jazamatronic/nucleo_adsr/Core/Src/envelope.c

/*
 * MIT License
 *
 * Copyright (c) 2021 Jared Anderson
 *
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
 * THE SOFTWARE IS PROVIDED "AS IS", WITHOUT WARRANTY OF ANY KIND, EXPRESS OR
 * IMPLIED, INCLUDING BUT NOT LIMITED TO THE WARRANTIES OF MERCHANTABILITY,
 * FITNESS FOR A PARTICULAR PURPOSE AND NONINFRINGEMENT. IN NO EVENT SHALL THE
 * AUTHORS OR COPYRIGHT HOLDERS BE LIABLE FOR ANY CLAIM, DAMAGES OR OTHER
 * LIABILITY, WHETHER IN AN ACTION OF CONTRACT, TORT OR OTHERWISE, ARISING FROM,
 * OUT OF OR IN CONNECTION WITH THE SOFTWARE OR THE USE OR OTHER DEALINGS IN THE
 * SOFTWARE.
 */

#include "envelope.h"

// tclsh for linear segment: for {set i 1} { $i <= 256 } { incr i } { puts [format "0x%03x" [expr int(($i / 256.0) * 4095)]] }
//           exp    segment: for {set i 1} { $i <= 256 } { incr i } { puts [format "0x%03x" [expr int(pow(4095, ($i / 256.0)))]] }
//           log    segment: for {set i 1} { $i <= 256 } { incr i } { puts [format "0x%03x" [expr int(log10(1 + (9 * ($i/256.0))) * 4095)]] }
static uint16_t adsr_curves[NUM_CURVES][ADSR_TABLE_LEN] = { \
  {0x00f, 0x01f, 0x02f, 0x03f, 0x04f, 0x05f, 0x06f, 0x07f, 0x08f, 0x09f, 0x0af, \
  0x0bf, 0x0cf, 0x0df, 0x0ef, 0x0ff, 0x10f, 0x11f, 0x12f, 0x13f, 0x14f, 0x15f, \
  0x16f, 0x17f, 0x18f, 0x19f, 0x1af, 0x1bf, 0x1cf, 0x1df, 0x1ef, 0x1ff, 0x20f, \
  0x21f, 0x22f, 0x23f, 0x24f, 0x25f, 0x26f, 0x27f, 0x28f, 0x29f, 0x2af, 0x2bf, \
  0x2cf, 0x2df, 0x2ef, 0x2ff, 0x30f, 0x31f, 0x32f, 0x33f, 0x34f, 0x35f, 0x36f, \
  0x37f, 0x38f, 0x39f, 0x3af, 0x3bf, 0x3cf, 0x3df, 0x3ef, 0x3ff, 0x40f, 0x41f, \
  0x42f, 0x43f, 0x44f, 0x45f, 0x46f, 0x47f, 0x48f, 0x49f, 0x4af, 0x4bf, 0x4cf, \
  0x4df, 0x4ef, 0x4ff, 0x50f, 0x51f, 0x52f, 0x53f, 0x54f, 0x55f, 0x56f, 0x57f, \
  0x58f, 0x59f, 0x5af, 0x5bf, 0x5cf, 0x5df, 0x5ef, 0x5ff, 0x60f, 0x61f, 0x62f, \
  0x63f, 0x64f, 0x65f, 0x66f, 0x67f, 0x68f, 0x69f, 0x6af, 0x6bf, 0x6cf, 0x6df, \
  0x6ef, 0x6ff, 0x70f, 0x71f, 0x72f, 0x73f, 0x74f, 0x75f, 0x76f, 0x77f, 0x78f, \
  0x79f, 0x7af, 0x7bf, 0x7cf, 0x7df, 0x7ef, 0x7ff, 0x80f, 0x81f, 0x82f, 0x83f, \
  0x84f, 0x85f, 0x86f, 0x87f, 0x88f, 0x89f, 0x8af, 0x8bf, 0x8cf, 0x8df, 0x8ef, \
  0x8ff, 0x90f, 0x91f, 0x92f, 0x93f, 0x94f, 0x95f, 0x96f, 0x97f, 0x98f, 0x99f, \
  0x9af, 0x9bf, 0x9cf, 0x9df, 0x9ef, 0x9ff, 0xa0f, 0xa1f, 0xa2f, 0xa3f, 0xa4f, \
  0xa5f, 0xa6f, 0xa7f, 0xa8f, 0xa9f, 0xaaf, 0xabf, 0xacf, 0xadf, 0xaef, 0xaff, \
  0xb0f, 0xb1f, 0xb2f, 0xb3f, 0xb4f, 0xb5f, 0xb6f, 0xb7f, 0xb8f, 0xb9f, 0xbaf, \
  0xbbf, 0xbcf, 0xbdf, 0xbef, 0xbff, 0xc0f, 0xc1f, 0xc2f, 0xc3f, 0xc4f, 0xc5f, \
  0xc6f, 0xc7f, 0xc8f, 0xc9f, 0xcaf, 0xcbf, 0xccf, 0xcdf, 0xcef, 0xcff, 0xd0f, \
  0xd1f, 0xd2f, 0xd3f, 0xd4f, 0xd5f, 0xd6f, 0xd7f, 0xd8f, 0xd9f, 0xdaf, 0xdbf, \
  0xdcf, 0xddf, 0xdef, 0xdff, 0xe0f, 0xe1f, 0xe2f, 0xe3f, 0xe4f, 0xe5f, 0xe6f, \
  0xe7f, 0xe8f, 0xe9f, 0xeaf, 0xebf, 0xecf, 0xedf, 0xeef, 0xeff, 0xf0f, 0xf1f, \
  0xf2f, 0xf3f, 0xf4f, 0xf5f, 0xf6f, 0xf7f, 0xf8f, 0xf9f, 0xfaf, 0xfbf, 0xfcf, \
  0xfdf, 0xfef, 0xfff }, \
  {0x001, 0x001, 0x001, 0x001, 0x001, 0x001, 0x001, 0x001, 0x001, 0x001, 0x001, \
  0x001, 0x001, 0x001, 0x001, 0x001, 0x001, 0x001, 0x001, 0x001, 0x001, 0x002, \
  0x002, 0x002, 0x002, 0x002, 0x002, 0x002, 0x002, 0x002, 0x002, 0x002, 0x002, \
  0x003, 0x003, 0x003, 0x003, 0x003, 0x003, 0x003, 0x003, 0x003, 0x004, 0x004, \
  0x004, 0x004, 0x004, 0x004, 0x004, 0x005, 0x005, 0x005, 0x005, 0x005, 0x005, \
  0x006, 0x006, 0x006, 0x006, 0x007, 0x007, 0x007, 0x007, 0x007, 0x008, 0x008, \
  0x008, 0x009, 0x009, 0x009, 0x00a, 0x00a, 0x00a, 0x00b, 0x00b, 0x00b, 0x00c, \
  0x00c, 0x00d, 0x00d, 0x00d, 0x00e, 0x00e, 0x00f, 0x00f, 0x010, 0x010, 0x011, \
  0x012, 0x012, 0x013, 0x013, 0x014, 0x015, 0x015, 0x016, 0x017, 0x018, 0x018, \
  0x019, 0x01a, 0x01b, 0x01c, 0x01d, 0x01e, 0x01f, 0x020, 0x021, 0x022, 0x023, \
  0x024, 0x026, 0x027, 0x028, 0x029, 0x02b, 0x02c, 0x02e, 0x02f, 0x031, 0x032, \
  0x034, 0x036, 0x038, 0x03a, 0x03b, 0x03d, 0x03f, 0x042, 0x044, 0x046, 0x048, \
  0x04b, 0x04d, 0x050, 0x052, 0x055, 0x058, 0x05b, 0x05e, 0x061, 0x064, 0x068, \
  0x06b, 0x06f, 0x072, 0x076, 0x07a, 0x07e, 0x082, 0x087, 0x08b, 0x090, 0x094, \
  0x099, 0x09e, 0x0a4, 0x0a9, 0x0af, 0x0b4, 0x0ba, 0x0c1, 0x0c7, 0x0ce, 0x0d4, \
  0x0db, 0x0e3, 0x0ea, 0x0f2, 0x0fa, 0x102, 0x10b, 0x114, 0x11d, 0x126, 0x130, \
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
};


/*
 * process an envelope
 *
 * Walks through the phases of an ADSR in the following way:
 *
 *   Start in the idle state.  If gate is low, stay in idle.
 *   If gate is high, start the attack phase.
 *   While in the attack state, index the table until the end in the time given by attack.
 *   If gate goes low during attack phase, move directly to release.
 *   If attack finishes, move to decay state.
 *   Decay moves from max to sustain value in the given decay time
 *   If gate goes low during decay phase, move directly to release.
 *   If decay finishes, if sustain is zero move to idle, otherwise move to sustain state.
 *
 *   When an envelope is done we set the end flag to trigger other envs if needed
 *
 *   Sustain state holds that value while gate is high. On gate low move to release state
 *   In release state, move from sustain down to 0 in the time given by release.
 *   Once release is completed move to idle
 *   If gate goes high during release phase, restart the attack phase (TODO: make it restart from where it is, not 0)
 *
 *   For calculating durations - assumption is we're doing 10kHz sampling with a table length of 256 entries
 *   Time between samples will be 0.1ms so 256 entries gives 25ms or so as the fastest transition
 *   Care must be taken with an adc value of 0 - it should mean a phase_inc of a single step
 *
 *   
 *   Let's say we have full adc range = 5s (60s is tooo long)
 *   @ 10kHz that equals 50k samples 
 *
 *
 *   full scale adc = 4095
 *   table length of 256 / number of samples for 5s (50k) = 0.0512
 *   phase_inc = (4095 / <adc_value>) * 0.0512
 *
 *   doesnt return anything, the value to write to the DAC is stored in the envelope - should be 12 bit right aligned values from the tables
 *
 *   Adding loop modes which do AD loops repeat - sustain level will be used as time between repeats
 *
 *   TRIG or INV_TRIG modes - AD oneshot envelope
 *    At the end of its cycle, a triggering envelope will be used to trigger a simple AD of another envelope
 *    The triggered envelope will ignore all gate information and do a single cycle
 *    env0 triggers env1, env1 triggers env2 and env2 triggers env0 - maybe there's a way to get them in a loop, not sure
 *    The RGB led will show two of three colours to show that the envelope is in trigger mode - the selected env plus the triggering env will be lit
 *    inverted trigger mode will have the two leds, but flashing
 *   
 *   LMNC bouncing ball easter egg mode
 *    A = initial height -> full scale = 4m
 *    D = rebound -> FS = 2
 *    R = gravity -> FS = 2 * Gravity which is -9.8 ms^-2 - as we're updating at ~10kHz this should meters per 0.1ms
 *    Do the math for the height in phase, store the velocity in phase_inc - cast it into val at the end
 *    Get into bouncing ball mode by using long press and moving sustain until it's at the top of its range (blue led)
 *    Coming out of bounce goes straight to oneshot
 */
void process_env(env_gen_t *env, uint16_t gate, uint16_t trigger)
{
  // default to staying exactly where we are
  enum state next_state = env->current_state;

  // check to see if we're triggered
  if (TRIG_MODE(env) && trigger) {
    env->triggered = 1;
  }

  // clear end of env flag
  if (env->end) {
    env->end = 0;
  }

  switch (env->current_state) {

    case IDLE:
      if (!GATE(env, gate)) { 
	env->val = 0;
      } else {
	//start the ball rolling
	if (env->mode == BOUNCY) {
	  next_state = BOUNCE;
	  //attack is initial height
	  env->phase = env->adsr[ATTACK];
	  env->val = env->adsr[ATTACK]; 
	} else {
	  next_state = ATTACK;
	  env->phase = 0;	
	}
      }
      break;

    case ATTACK:
      //gate == 0 && !env->triggered
      if (!GATE(env, gate)) { 
	env->phase = (uint16_t)ADSR_TABLE_LEN - 1;
	env->release_from = env->val;
	next_state = RELEASE;
      } else {
	if (env->adsr[ATTACK] > 0) {
	  env->phase_inc = ((float32_t)ADSR_TABLE_LEN / (LONGEST_PHASE_S * ENV_SR)) * (ADC_FS / env->adsr[ATTACK]);
	} else {
	  //attack is zero, phase_inc is twice what it would be if it were one
	  env->phase_inc = ((float32_t)ADSR_TABLE_LEN / (LONGEST_PHASE_S * ENV_SR)) * 2 * ADC_FS;
	}
	env->phase += env->phase_inc;
	if (env->phase > ADSR_TABLE_LEN) {
	  env->phase = (uint16_t)ADSR_TABLE_LEN - 1;
	  env->val = ADC_FS;
	  next_state = DECAY;
	} else {
	  env->val = interp_adsr_seg(env->acurve, env->phase);
	}
      }
      break;

    case DECAY:
      if (!GATE(env, gate)) { 
	env->phase = (uint16_t)ADSR_TABLE_LEN - 1;
	env->release_from = env->val;
	next_state = RELEASE;
      } else {
	if (env->adsr[DECAY] > 0) {
	  env->phase_inc = ((float32_t)ADSR_TABLE_LEN / (LONGEST_PHASE_S * ENV_SR)) * (ADC_FS / env->adsr[DECAY]);
	} else {
	  //decay is zero, phase_inc is twice what it would be if it were one
	  env->phase_inc = ((float32_t)ADSR_TABLE_LEN / (LONGEST_PHASE_S * ENV_SR)) * 2 * ADC_FS;
	}
	env->phase -= env->phase_inc;
	if (env->phase < 0) {
	  next_state = SUSTAIN;
	  if (LOOP_MODE(env)) {
	    env->phase = 0;
	    env->val = 0;
	    // maybe having loop modes signal the end of their AD cycle can be interesting - we will have looping triggers?
	    env->end = 1;
	  } else if (TRIG_MODE(env)) {
	    env->phase = 0;
	    env->val = 0;
	    env->triggered = 0;
	    env->end = 1;
	    next_state = IDLE;
	  } else {
	    env->val = env->adsr[SUSTAIN];
	  }
	} else {
	  if (ONES_MODE(env)) {
	    env->val = (uint16_t)(env->adsr[SUSTAIN] + ((ADC_FS - env->adsr[SUSTAIN]) * (interp_adsr_seg(env->dcurve, env->phase) / (float32_t)ADC_FS)));
	  } else {
	    env->val = interp_adsr_seg(env->dcurve, env->phase);
	  }
	}
      }
      break;

    case SUSTAIN:
      if (!GATE(env, gate)) { 
	env->phase = (uint16_t)ADSR_TABLE_LEN - 1;
	env->release_from = env->adsr[SUSTAIN];
	if (LOOP_MODE(env)) {
	  //have it trigger each time it finishes its AD cycle, not when the gate goes off
	  //env->end = 1;
	  next_state = IDLE;
	} else {
	  next_state = RELEASE;
	}
      } else if (LOOP_MODE(env)) {
	if (env->adsr[SUSTAIN] > 0) {
	  env->phase_inc = ((float32_t)ADSR_TABLE_LEN / (LONGEST_PHASE_S * ENV_SR)) * (ADC_FS / env->adsr[SUSTAIN]);
	} else {
	  //sustain is zero, phase_inc is twice what it would be if it were one
	  env->phase_inc = ((float32_t)ADSR_TABLE_LEN / (LONGEST_PHASE_S * ENV_SR)) * 2 * ADC_FS;
	}
	env->phase += env->phase_inc;
	if (env->phase > ADSR_TABLE_LEN) {
	  next_state = ATTACK;
	  env->phase = 0;	
	}
      }
      break;

    case RELEASE:
      if (GATE(env, gate)) { 
	next_state = ATTACK;
      } else {
	if (env->adsr[SUSTAIN] == 0) {
	  // skip right to idle if sustain is 0
	  env->end = 1;
	  next_state = IDLE;
	  env->val = 0;
	} else {
	  if (env->adsr[RELEASE] > 0) {
	    env->phase_inc = ((float32_t)ADSR_TABLE_LEN / (LONGEST_PHASE_S * ENV_SR)) * (ADC_FS / env->adsr[RELEASE]);
	  } else {
	    //release is zero, phase_inc is twice what it would be if it were one
	    env->phase_inc = ((float32_t)ADSR_TABLE_LEN / (LONGEST_PHASE_S * ENV_SR)) * 2 * ADC_FS;
	  }
	  env->phase -= env->phase_inc;
	  if (env->phase <= 0) {
	    env->phase = 0;
	    env->val = 0;
	    env->end = 1;
	    next_state = IDLE;
	  } else {
	    env->val = (uint16_t)(env->release_from * (interp_adsr_seg(env->rcurve, env->phase) / (float32_t)ADC_FS));
	  }
	}
      }
      break;

    case BOUNCE:
      if (!GATE(env, gate)) { 
	// shut it down as soon as the gate goes off
	next_state = IDLE;
	env->val = 0;
      } else {
	env->phase_inc += (2 * ((float32_t)env->adsr[RELEASE] / ADC_FS) * GRAVITY); // phase_inc is the velocity, increment it by gravity
	env->phase += env->phase_inc;						    // calculate our new height - add velocity to our current position
	// if height is less than zero it means we've hit the ground - bounce by reversing our velocity and multiplying it by our rebound factor
	if (env->phase <= 0) {
	  env->phase = 0;
	  env->phase_inc *= (-2 * ((float32_t)env->adsr[DECAY] / ADC_FS));
	}
	//finally - it's all done - put it into the value that goes to the dac.
	env->val = (uint16_t)env->phase;
      }
      break;

    default:
	// We should never get here.
	next_state = IDLE;
	env->val = 0;
	break;
  }

  //shouldn't have to do this - but maybe things go heywire - a distinct possibility in bouncing ball mode
  if (env->val > ADC_FS) { env->val = ADC_FS; }
  env->current_state = next_state;

}

/*
 * Inits an envelope
 * sets most things to zero
 */
void init_env(env_gen_t *env) {
  env->val = 0;
  env->mode = ONESHOT;
  env->adsr[ATTACK] = 0;
  env->adsr[DECAY] = 0;
  env->adsr[SUSTAIN] = 0;
  env->adsr[RELEASE] = 0;
  env->release_from = 0;
  env->triggered = 0;
  env->end = 0;
  env->phase = 0;
  env->phase_inc = 0;
  env->current_state = IDLE;
  env->acurve = LIN;
  env->dcurve = EXP;
  env->rcurve = EXP;
}

uint16_t interp_adsr_seg(enum curves curve, float32_t phase) {

  uint16_t idx = phase;

  if (idx >= ADSR_TABLE_LEN) {
    idx = ADSR_TABLE_LEN - 1;
  }

  uint16_t next_idx = idx + 1;
  float32_t r = phase - idx;
  uint16_t s0, s1, sf;

  s0 = adsr_curves[curve][idx];

  if (next_idx >= ADSR_TABLE_LEN) {
    s1 = adsr_curves[curve][ADSR_TABLE_LEN - 1];
  } else {
    s1 = adsr_curves[curve][next_idx];
  }
  sf = (uint16_t)(s0 + r * (s1 - s0));

  return sf;
}
